DerGary/all-in-one-sensor-device/Ultimate/images/1f249b83a3ead3f2.webp

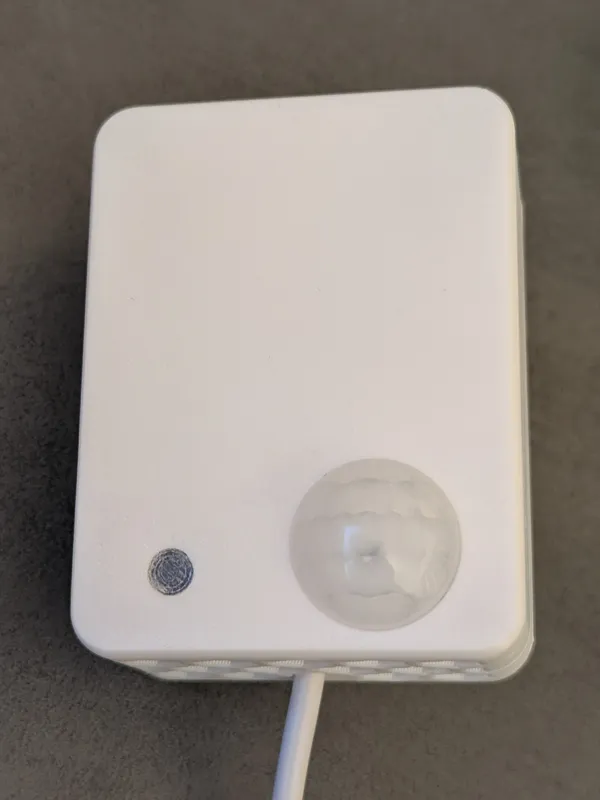
Ultimate/images/1f249b83a3ead3f2.webp
