DerGary/all-in-one-sensor-device/Ultimate/images/4ef361136f98375c.webp

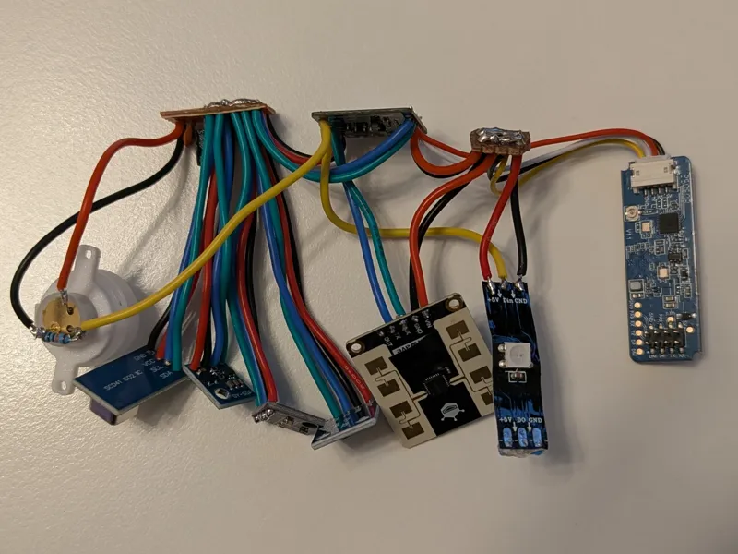
Ultimate/images/4ef361136f98375c.webp
