DerGary/all-in-one-sensor-device/Ultimate/images/97fdcc9fb1d8076a.webp

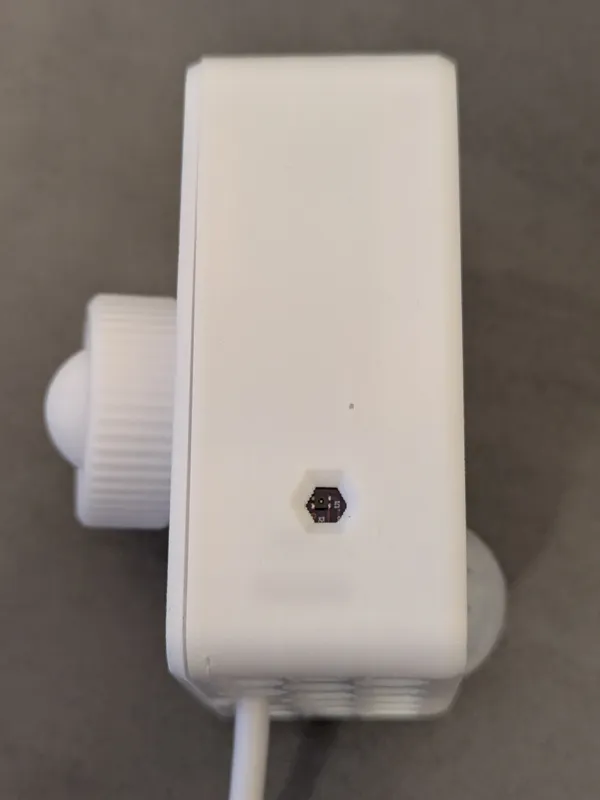
Ultimate/images/97fdcc9fb1d8076a.webp
