DerGary/all-in-one-sensor-device/Ultimate/images/203b10911fffc19c.webp

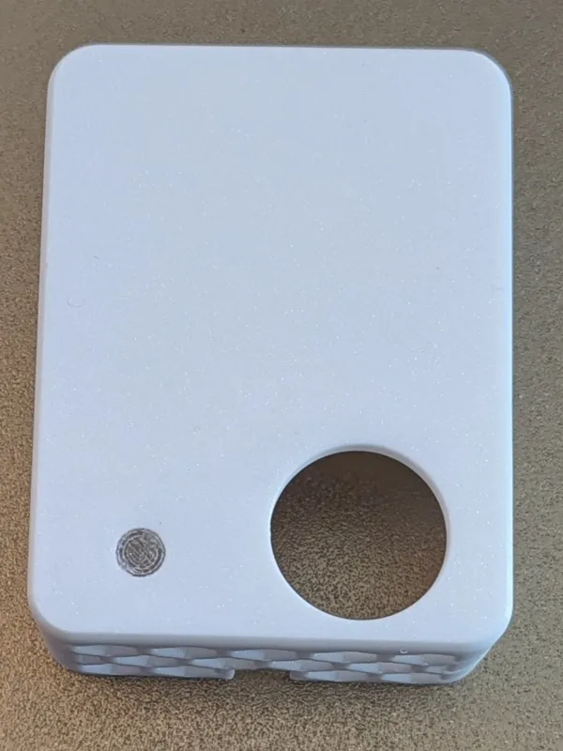
Ultimate/images/203b10911fffc19c.webp
