DerGary/all-in-one-sensor-device/Ultimate/images/04825b5d137e8ed2.webp

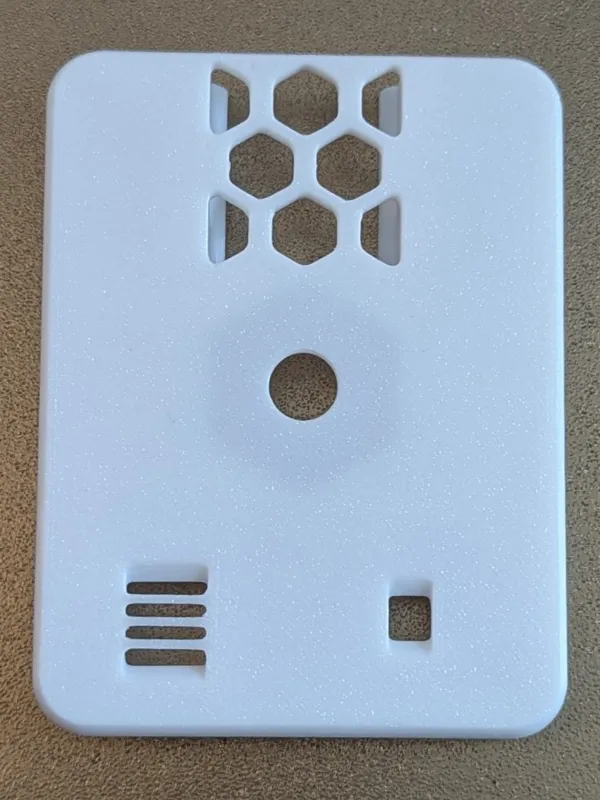
Ultimate/images/04825b5d137e8ed2.webp
