DerGary/all-in-one-sensor-device/Ultimate/images/b3074d54446aa099.webp

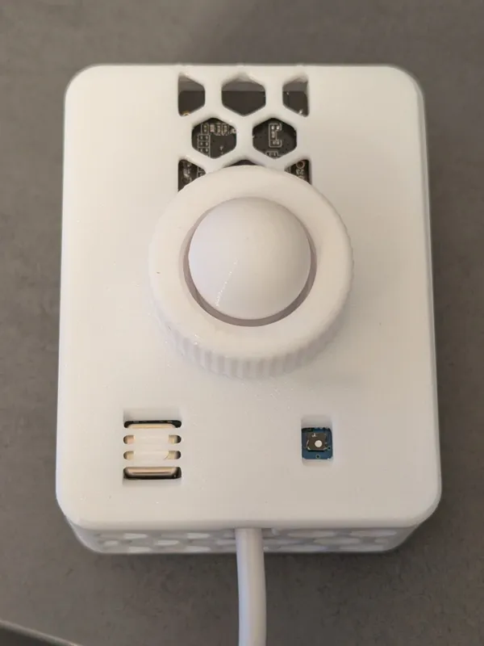
Ultimate/images/b3074d54446aa099.webp
