DerGary/all-in-one-sensor-device/Ultimate/images/ce54352bc6cfa1f4.webp

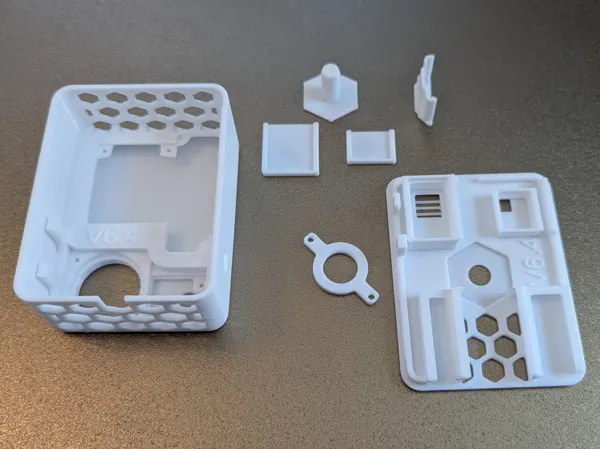
Ultimate/images/ce54352bc6cfa1f4.webp
