DerGary/all-in-one-sensor-device/Ultimate/images/PXL_20260617_181902793.jpg

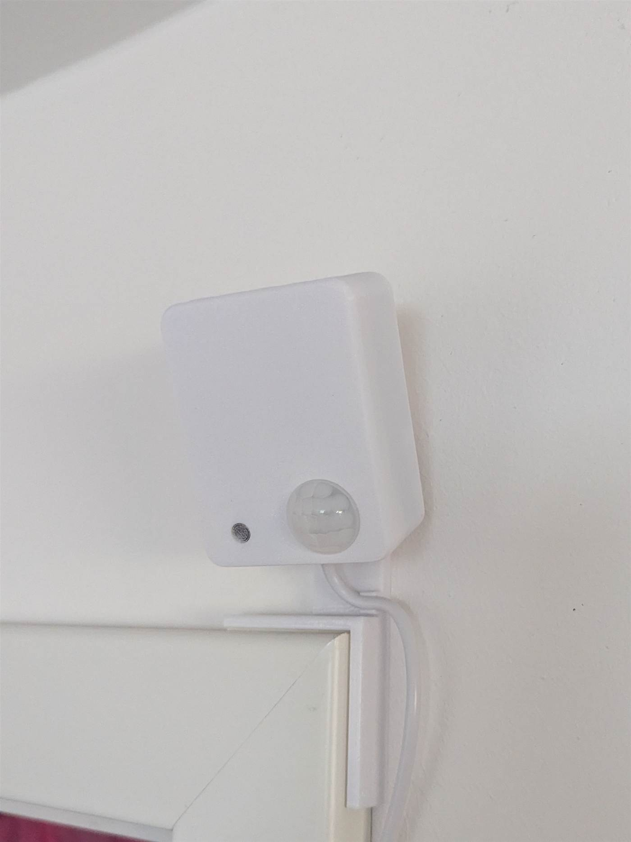
Ultimate/images/PXL_20260617_181902793.jpg
