DerGary/all-in-one-sensor-device/Ultimate/images/PXL_20260617_181915556.jpg

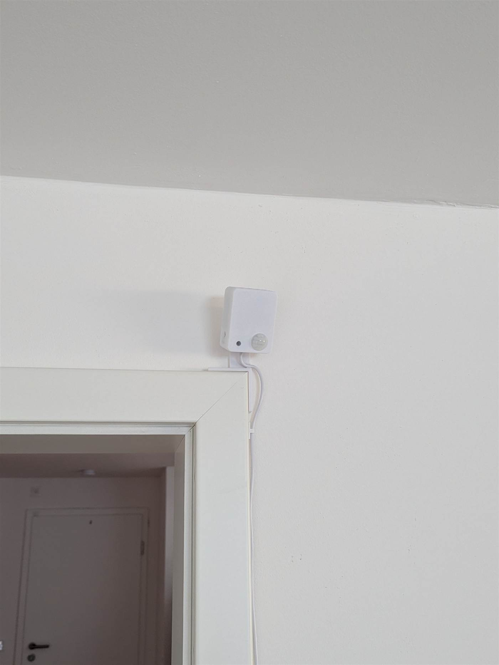
Ultimate/images/PXL_20260617_181915556.jpg
