DerGary/all-in-one-sensor-device/Ultimate/images/PXL_20260617_181952824~2.jpg

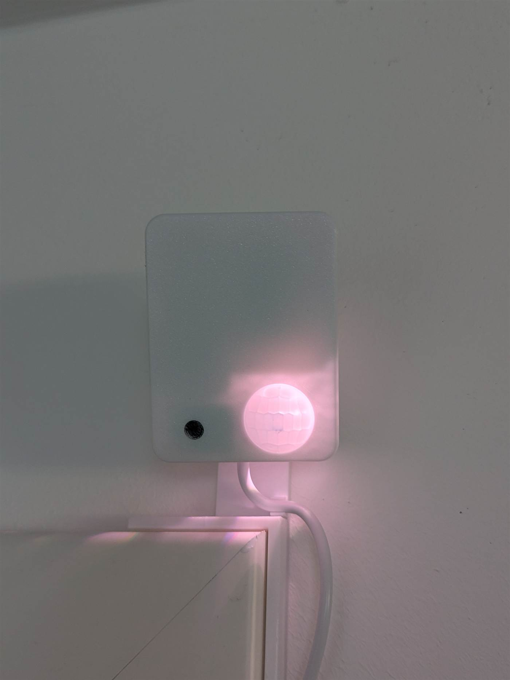
Ultimate/images/PXL_20260617_181952824~2.jpg
