DerGary/all-in-one-sensor-device/Ultimate/images/PXL_20260617_182021402~2.jpg

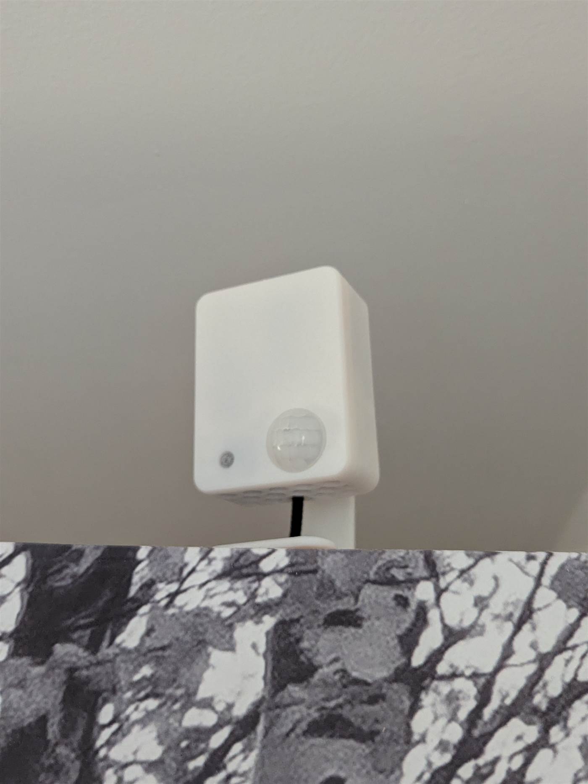
Ultimate/images/PXL_20260617_182021402~2.jpg
