DerGary/all-in-one-sensor-device/V2.1/images/BackD1Mini.jpg

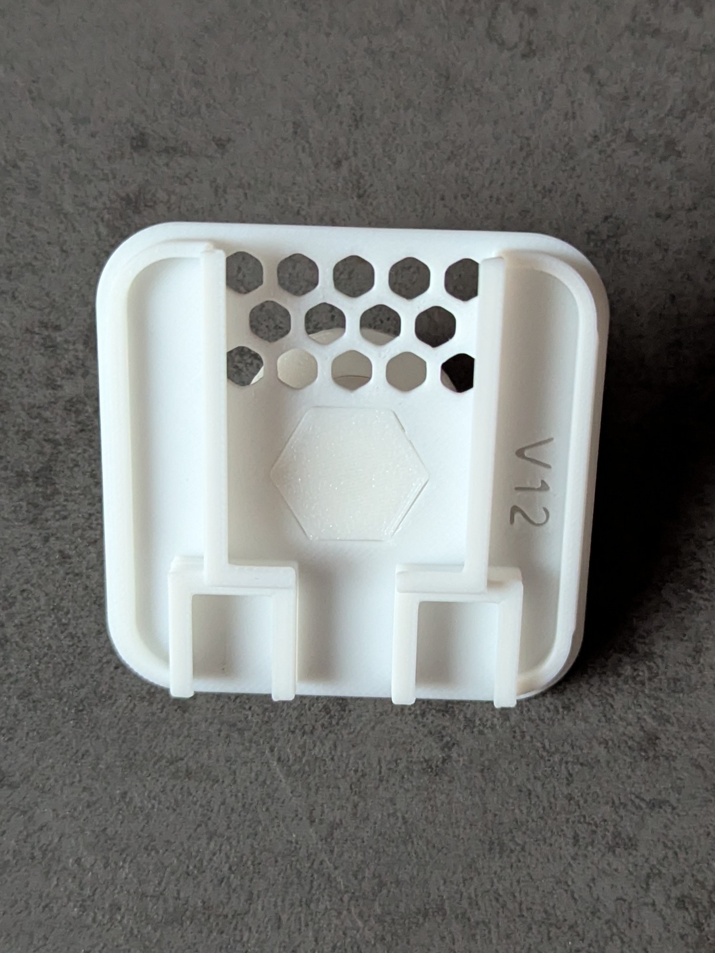
V2.1/images/BackD1Mini.jpg
