DerGary/all-in-one-sensor-device/V2.1/images/BackLarge.jpg

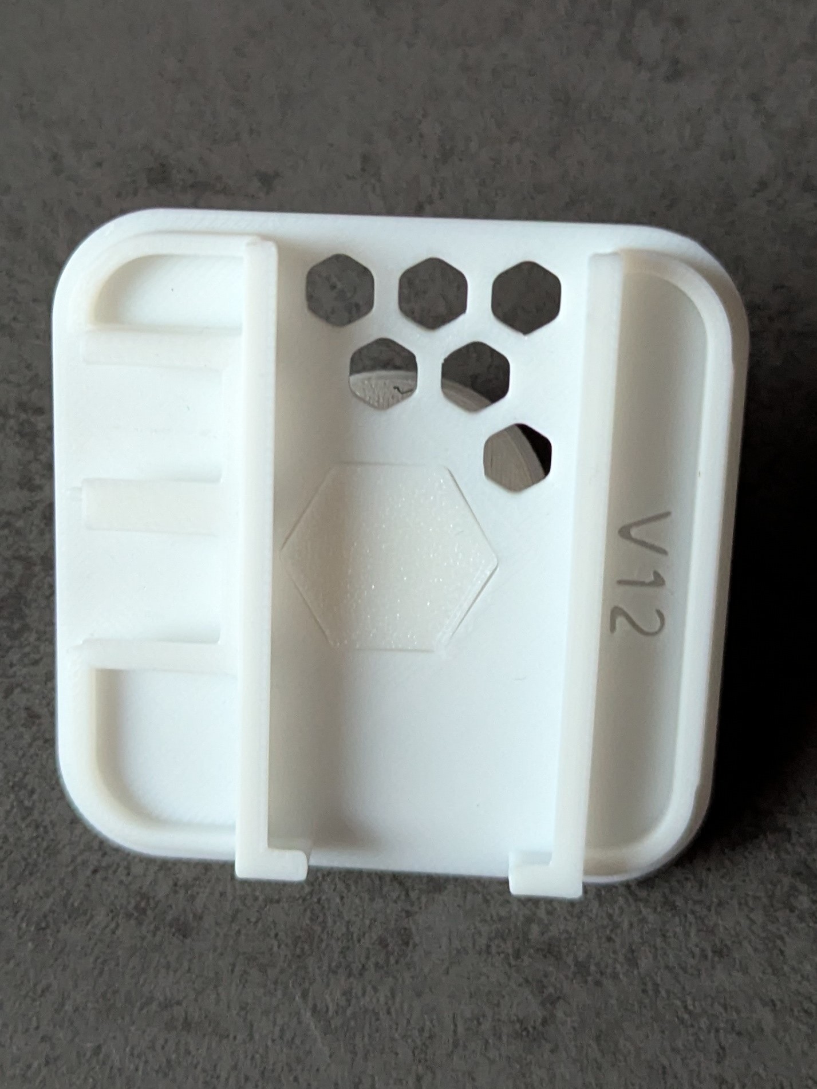
V2.1/images/BackLarge.jpg
