DerGary/all-in-one-sensor-device/V2.1/images/BackSuperMini.jpg

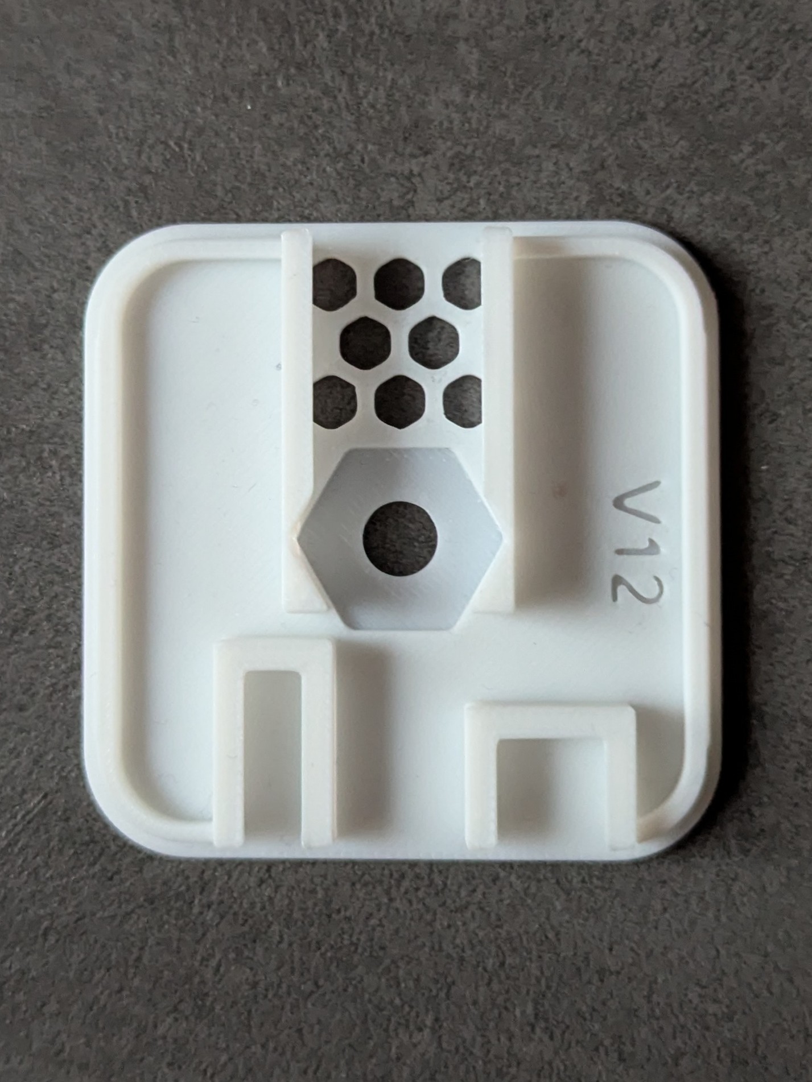
V2.1/images/BackSuperMini.jpg
