DerGary/all-in-one-sensor-device/V2.1/images/FrontEmptyBack.jpg

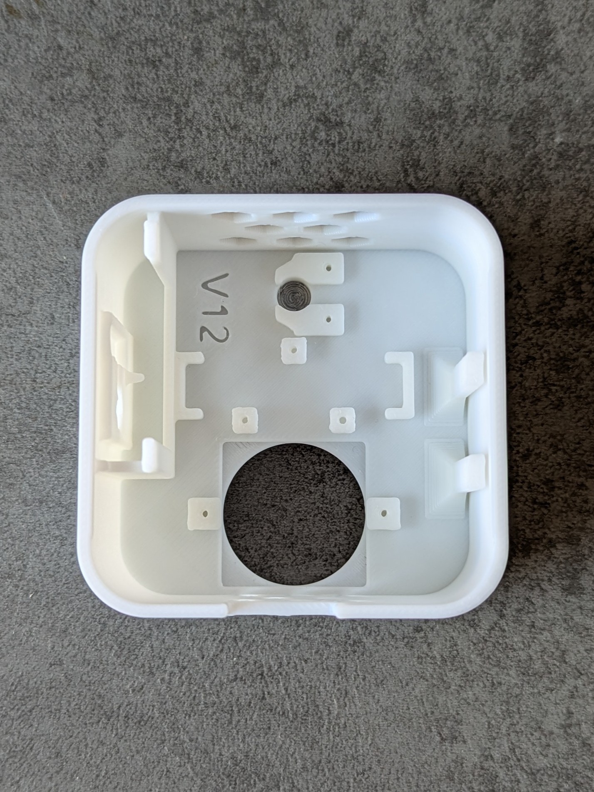
V2.1/images/FrontEmptyBack.jpg
