DerGary/all-in-one-sensor-device/V2.1/images/FrontEmptyFront.jpg

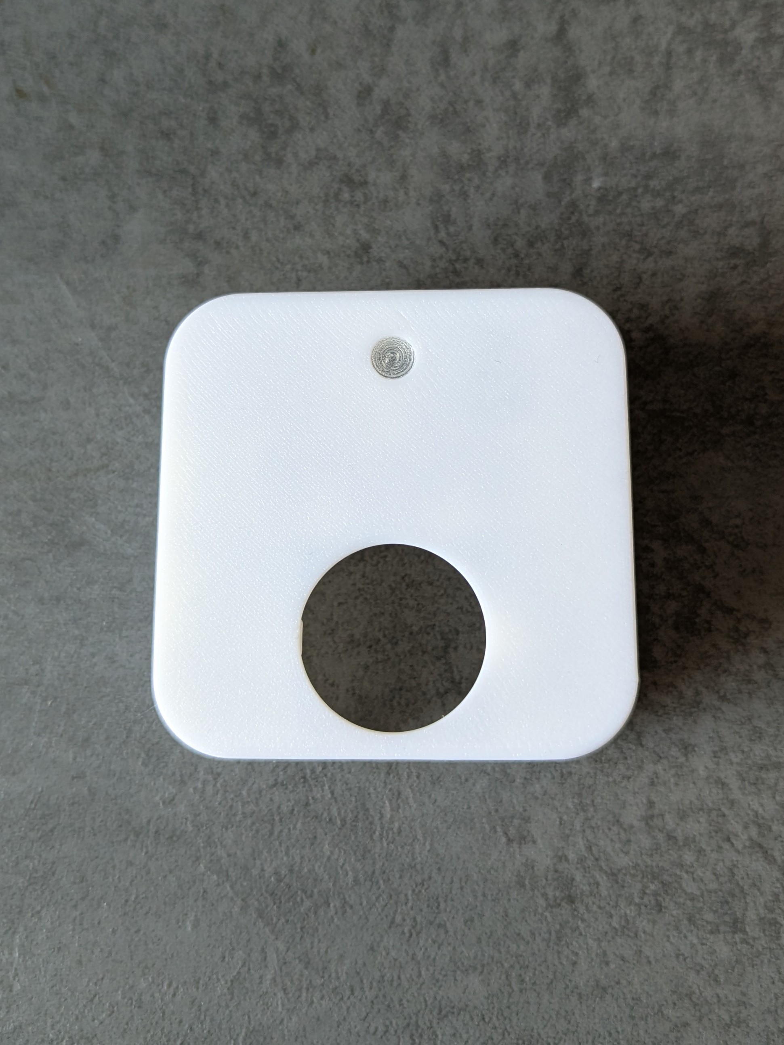
V2.1/images/FrontEmptyFront.jpg
