DerGary/all-in-one-sensor-device/V2.1/images/PXL_20260525_182911697.jpg

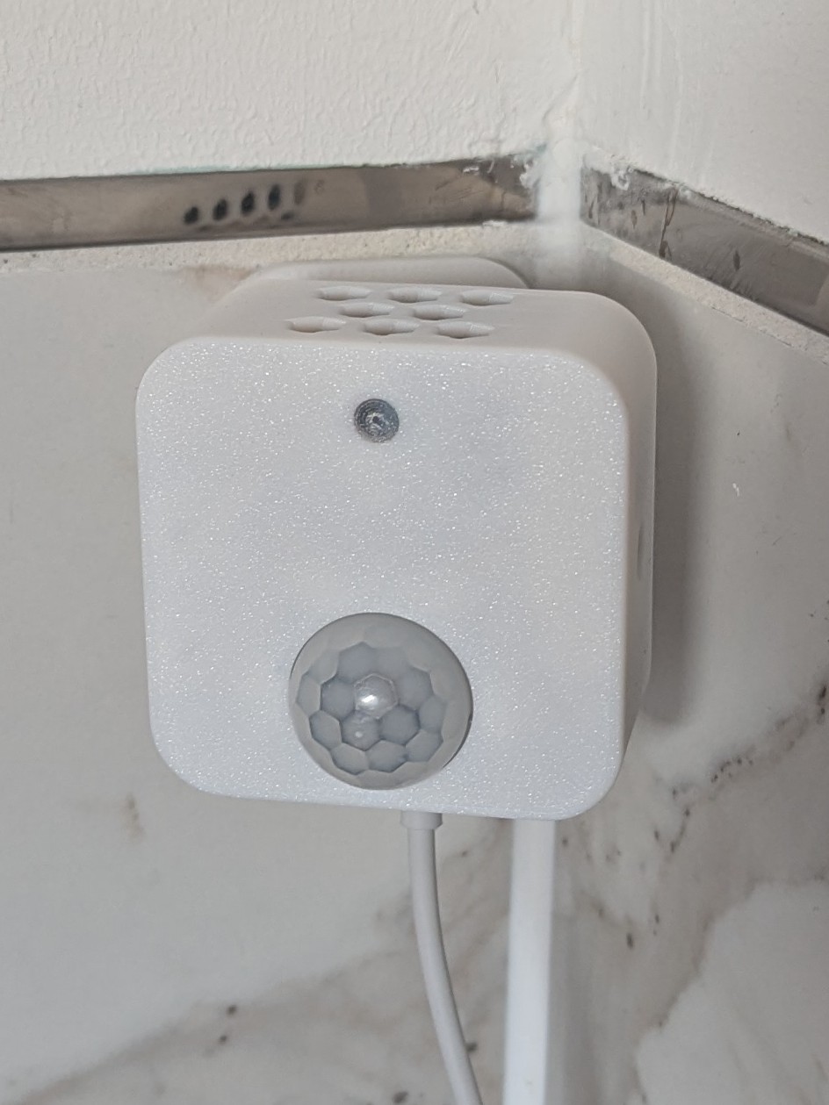
V2.1/images/PXL_20260525_182911697.jpg
