DerGary/all-in-one-sensor-device/V2.1/images/PXL_20260525_184815071.jpg

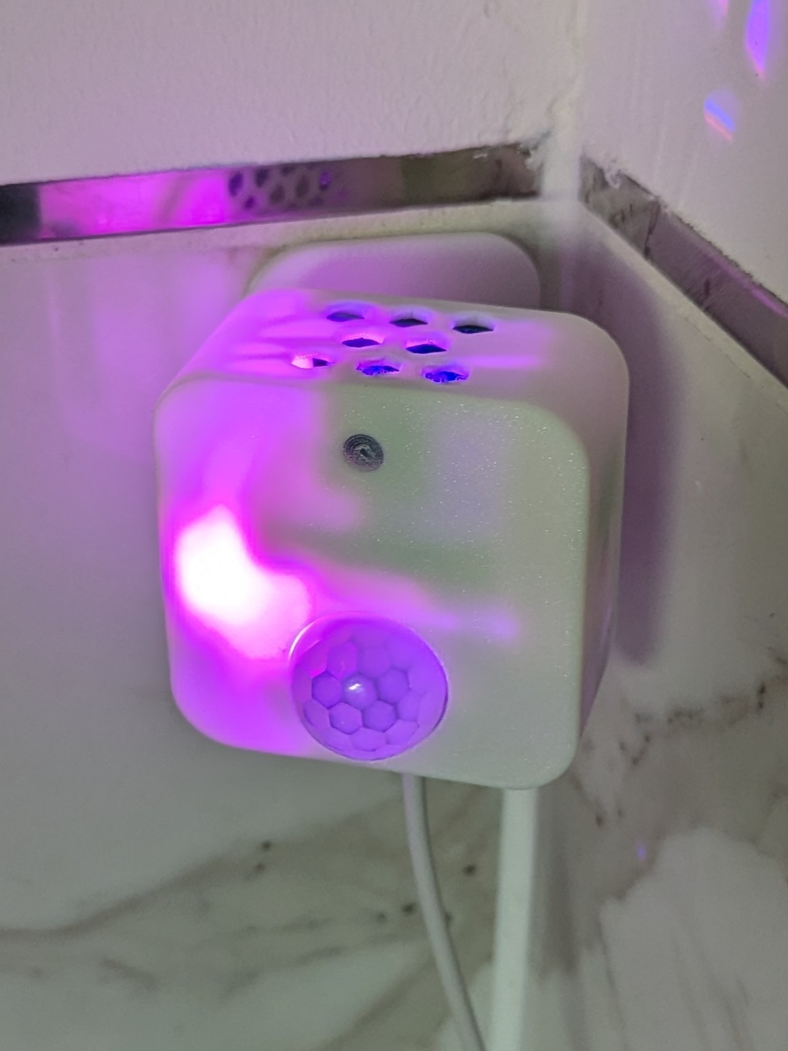
V2.1/images/PXL_20260525_184815071.jpg
