DerGary/all-in-one-sensor-device/V2/changelog.md

### V2.0.3

1. Add OpenThread as a connectivity alternative to WiFi (contributed by [TheDiffi](https://github.com/TheDiffi), [#6](https://github.com/DerGary/all-in-one-sensor-device/pull/6))
1. Update ESPHome to 2026.7

### V2.0.0

1. 3 different versions for different boards
    - Version for the ESP32 D1 Mini (no need to desolder the pins anymore 🥳).
    - Version for the ESP32 Super Mini (it should work with ESP32 C3/C6/S3, but i only tested it with the C6)
    - Version for the ESP32 Large Version
1. No need for jumper headers and wires / everything is soldered so it is a more secure connection
1. Separated wifi antenna and motion sensor farther apart to reduce false positive detections
1. Incorporate the ball head mount into the design, which is fully printable now and does not need a screw anymore.
1. The brightness sensor shield is now a solid part of the body. To print it you need an AMS or you have to remove that part before printing.
1. Tweaked the software
    - easier calibration experience
    - use of esp-idf framework which results in way less memory usage, so more features can be activated
    - added captive portal out of the box
    - german and english variant
    - used other uart pins, because using the uart0 will hinder from flashing the device via usb
